FBS93/STM32WLE5_RF_dongle/sw/arch/sw_parameters.md

# sw_parameters

## SW_ARCH_PARAMETER_1

Name: swp_rfSemanticParameters

Parameter inherited from upstream definition.

Upstream traceability:
- [SW_REQ_PARAMETER_1](../req/sw_parameters.md#sw_req_parameter_1)

Status: approved
