FBS93/STM32WLE5_RF_dongle/sys/arch/sys_interfaces.md

# sys_interfaces

## SYS_ARCH_INTERFACE_1

Name: sysi_usbExternal

Interface inherited from upstream definition.

Upstream traceability:
- [SYS_REQ_INTERFACE_1](../req/sys_interfaces.md#sys_req_interface_1)

Status: approved

## SYS_ARCH_INTERFACE_2

Name: sysi_rfExternal

Interface inherited from upstream definition.

Upstream traceability:
- [SYS_REQ_INTERFACE_2](../req/sys_interfaces.md#sys_req_interface_2)

Status: approved
