FBS93/STM32WLE5_RF_dongle/sys/arch/sys_parameters.md

# sys_parameters

## SYS_ARCH_PARAMETER_1

Name: sysp_packetType

Parameter inherited from upstream definition.

Upstream traceability:
- [SYS_REQ_PARAMETER_1](../req/sys_parameters.md#sys_req_parameter_1)

Status: approved

## SYS_ARCH_PARAMETER_2

Name: sysp_rfFrequencyHz

Parameter inherited from upstream definition.

Upstream traceability:
- [SYS_REQ_PARAMETER_2](../req/sys_parameters.md#sys_req_parameter_2)

Status: approved

## SYS_ARCH_PARAMETER_3

Name: sysp_payloadLengthBytes

Parameter inherited from upstream definition.

Upstream traceability:
- [SYS_REQ_PARAMETER_3](../req/sys_parameters.md#sys_req_parameter_3)

Status: approved

## SYS_ARCH_PARAMETER_4

Name: sysp_loraSpreadingFactor

Parameter inherited from upstream definition.

Upstream traceability:
- [SYS_REQ_PARAMETER_4](../req/sys_parameters.md#sys_req_parameter_4)

Status: approved

## SYS_ARCH_PARAMETER_5

Name: sysp_loraBandwidthKHz

Parameter inherited from upstream definition.

Upstream traceability:
- [SYS_REQ_PARAMETER_5](../req/sys_parameters.md#sys_req_parameter_5)

Status: approved

## SYS_ARCH_PARAMETER_6

Name: sysp_loraCodingRate

Parameter inherited from upstream definition.

Upstream traceability:
- [SYS_REQ_PARAMETER_6](../req/sys_parameters.md#sys_req_parameter_6)

Status: approved

## SYS_ARCH_PARAMETER_7

Name: sysp_loraLowDataRateOptimize

Parameter inherited from upstream definition.

Upstream traceability:
- [SYS_REQ_PARAMETER_7](../req/sys_parameters.md#sys_req_parameter_7)

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

Status: approved

## SYS_ARCH_PARAMETER_47

Name: sysp_radioErrors

Parameter inherited from upstream definition.

Upstream traceability:
- [SYS_REQ_PARAMETER_47](../req/sys_parameters.md#sys_req_parameter_47)

Status: approved
