FBS93/STM32WLE5_RF_dongle/sw/req/sw_cli.md

# Software CLI requirements

# SW_REQ_CLI_1

The software shall provide the host-side CLI tool defined by the applicable system CLI requirements.

Validation criteria:
- Exercise the host-side CLI against each behavior defined by the traced system CLI requirements and verify conformance without adding behavior not defined by those requirements.

Upstream traceability:
- [SYS_REQ_CLI_1](../../sys/req/sys_cli.md#sys_req_cli_1)
- [SYS_REQ_CLI_2](../../sys/req/sys_cli.md#sys_req_cli_2)
- [SYS_REQ_CLI_3](../../sys/req/sys_cli.md#sys_req_cli_3)
- [SYS_REQ_CLI_4](../../sys/req/sys_cli.md#sys_req_cli_4)
- [SYS_REQ_CLI_5](../../sys/req/sys_cli.md#sys_req_cli_5)
- [SYS_REQ_CLI_6](../../sys/req/sys_cli.md#sys_req_cli_6)
- [SYS_REQ_CLI_7](../../sys/req/sys_cli.md#sys_req_cli_7)
- [SYS_ARCH_COMPONENT_2](../../sys/arch/sys_components.md#sys_arch_component_2)
- [SYS_ARCH_INTERFACE_1](../../sys/arch/sys_interfaces.md#sys_arch_interface_1)

References:
- [SW_REQ_INTERFACE_1](sw_interfaces.md#sw_req_interface_1)

Status: approved
