FBS93/STM32WLE5_RF_dongle/sw/req/sw_interfaces.md

# Software interfaces

# SW_REQ_INTERFACE_1

Name: swi_hostUsbControl

The software shall implement the host-control interface defined by [SYS_REQ_INTERFACE_1](../../sys/req/sys_interfaces.md#sys_req_interface_1).

Upstream traceability:
- [SYS_REQ_INTERFACE_1](../../sys/req/sys_interfaces.md#sys_req_interface_1)
- [SYS_ARCH_INTERFACE_1](../../sys/arch/sys_interfaces.md#sys_arch_interface_1)
- [SYS_ARCH_COMPONENT_1](../../sys/arch/sys_components.md#sys_arch_component_1)
- [SYS_ARCH_COMPONENT_2](../../sys/arch/sys_components.md#sys_arch_component_2)
- [HW_SW_INTERFACE_7](../../hw/cross_domain_interfaces/hw_sw_interface.md#hw_sw_interface_7)

Status: approved

# SW_REQ_INTERFACE_2

Name: swi_rfInputOutput

The software shall provide the RF operation behavior through the RF interface defined by [SYS_REQ_INTERFACE_2](../../sys/req/sys_interfaces.md#sys_req_interface_2).

Upstream traceability:
- [SYS_REQ_INTERFACE_2](../../sys/req/sys_interfaces.md#sys_req_interface_2)
- [SYS_ARCH_INTERFACE_2](../../sys/arch/sys_interfaces.md#sys_arch_interface_2)
- [SYS_ARCH_COMPONENT_1](../../sys/arch/sys_components.md#sys_arch_component_1)
- [HW_SW_INTERFACE_9](../../hw/cross_domain_interfaces/hw_sw_interface.md#hw_sw_interface_9)
- [HW_SW_INTERFACE_10](../../hw/cross_domain_interfaces/hw_sw_interface.md#hw_sw_interface_10)
- [HW_SW_INTERFACE_12](../../hw/cross_domain_interfaces/hw_sw_interface.md#hw_sw_interface_12)

Status: approved
