FBS93/STM32WLE5_RF_dongle/hw/FBS_kicad_lib/3d_models/4_diode_SMD/D_0402_1005Metric.STEP

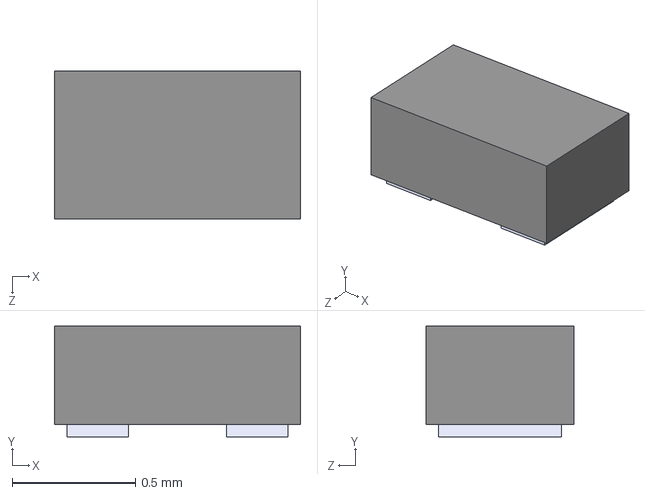
[picture p23: CAD file, 2024-11-07]
hw/FBS_kicad_lib/3d_models/4_diode_SMD/D_0402_1005Metric.STEP
1.00 x 0.45 x 0.6 mm
