FBS93/STM32WLE5_RF_dongle/hw/FBS_kicad_lib/3d_models/50_RF_filter/DLFCV-1000+.stp

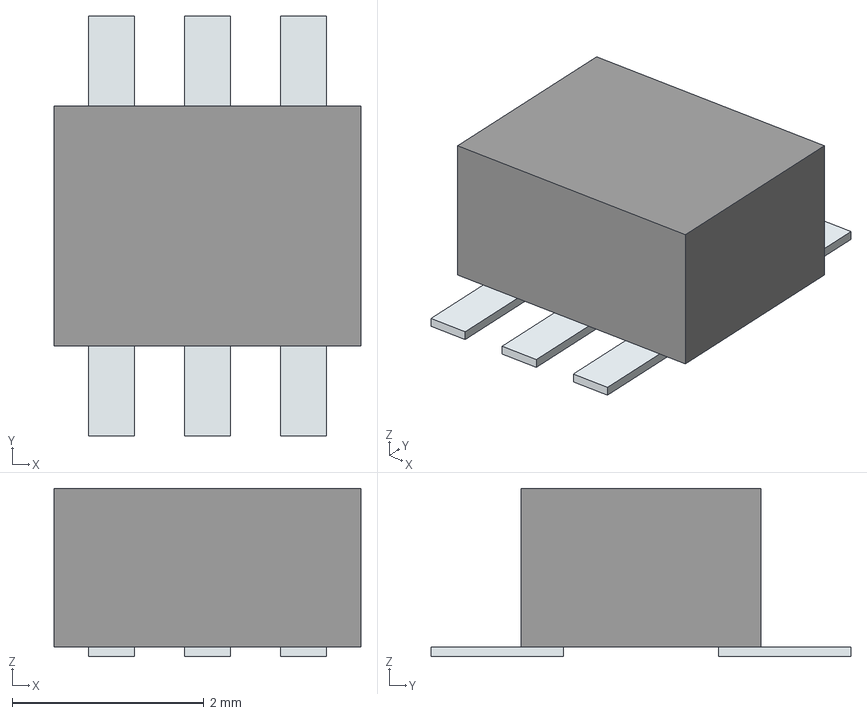
[picture p24: CAD file, 2024-11-07]
hw/FBS_kicad_lib/3d_models/50_RF_filter/DLFCV-1000+.stp
3.20 x 4.38 x 1.75 mm
Pins
