FBS93/STM32WLE5_RF_dongle/hw/FBS_kicad_lib/3d_models/5_balun_SMD/DXW21HN5011BL.stp

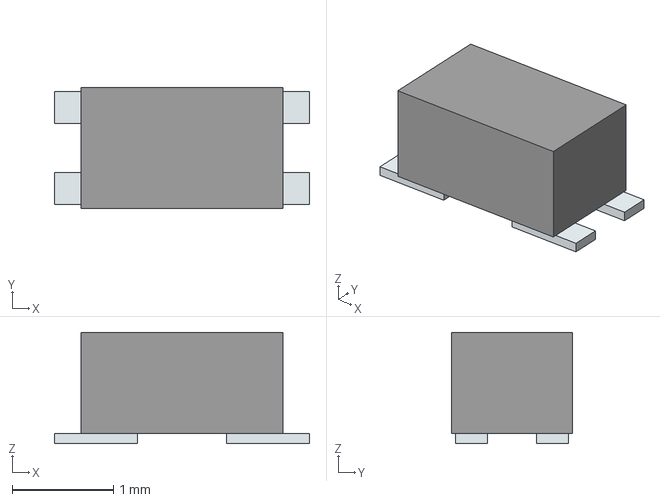
[picture p25: CAD file, 2024-11-07]
hw/FBS_kicad_lib/3d_models/5_balun_SMD/DXW21HN5011BL.stp
2.52 x 1.20 x 1.10 mm
Pins
