FBS93/STM32WLE5_RF_dongle/hw/FBS_kicad_lib/3d_models/60_RF_shield_clip/S0941_46R.stp

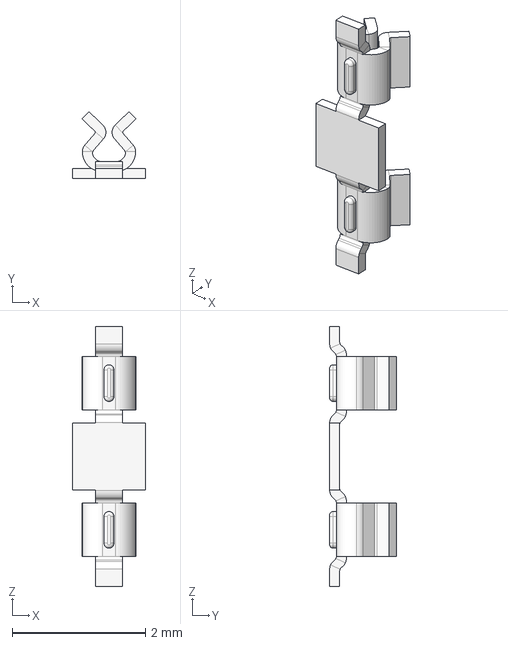
[picture p26: CAD file, 2024-11-07]
hw/FBS_kicad_lib/3d_models/60_RF_shield_clip/S0941_46R.stp
1.10 x 1.00 x 3.90 mm
