FBS93/STM32WLE5_RF_dongle/hw/FBS_kicad_lib/3d_models/6_fuse_SMD/0ZCM0020FF2G.stp

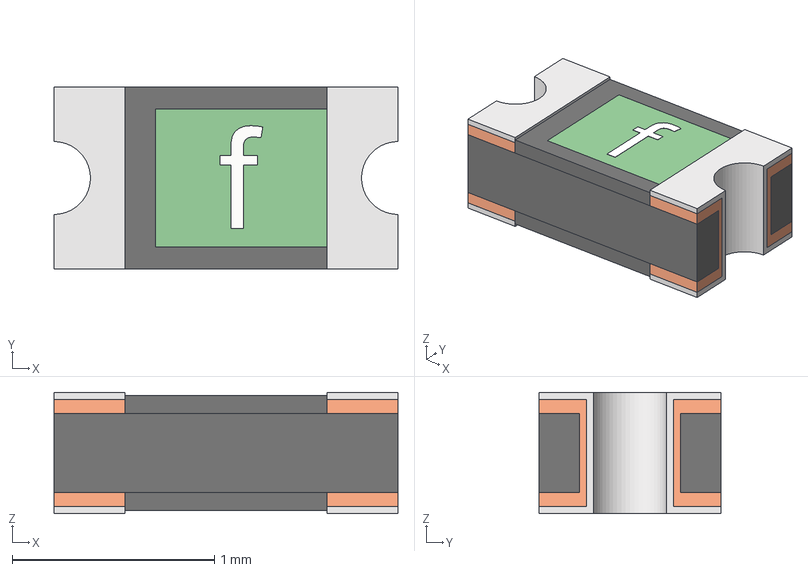
[picture p27: CAD file, 2024-11-07]
hw/FBS_kicad_lib/3d_models/6_fuse_SMD/0ZCM0020FF2G.stp
1.70 x 0.9 x 0.6 mm
0ZCM0020FF2G_PART1
0ZCM0020FF2G_PART2
0ZCM0020FF2G_PART3
0ZCM0020FF2G_PART4
0ZCM0020FF2G_PART5
0ZCM0020FF2G_PART6
0ZCM0020FF2G_PART7
0ZCM0020FF2G_PART8
0ZCM0020FF2G_PART9
0ZCM0020FF2G_PART10
0ZCM0020FF2G_PART11
