FBS93/STM32WLE5_RF_dongle/hw/FBS_kicad_lib/3d_models/105_SOT_package/SOT-23-3.step

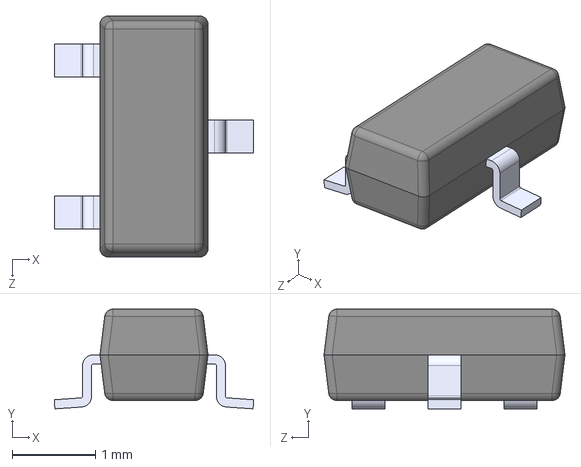
[picture p28: CAD file, 2024-11-07]
hw/FBS_kicad_lib/3d_models/105_SOT_package/SOT-23-3.step
2.40 x 1.20 x 2.90 mm
