FBS93/STM32WLE5_RF_dongle/hw/FBS_kicad_lib/3d_models/1_capacitor_SMD/C_1206_3216Metric.step

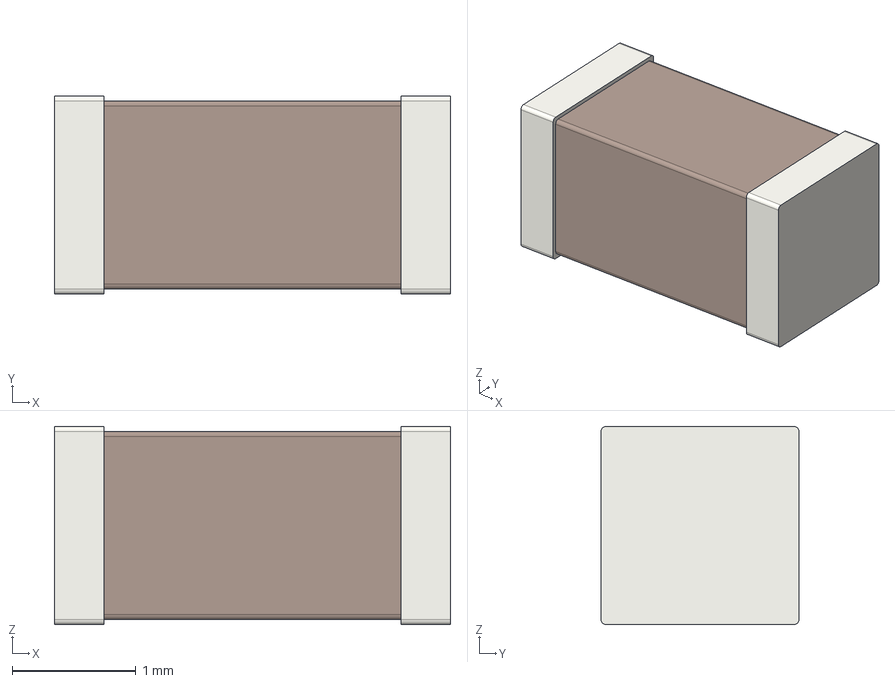
[picture p29: CAD file, 2024-11-07]
hw/FBS_kicad_lib/3d_models/1_capacitor_SMD/C_1206_3216Metric.step
3.20 x 1.60 x 1.60 mm
