FBS93/STM32WLE5_RF_dongle/hw/FBS_kicad_lib/3d_models/220_cortex-M_debug_connector/FTSH-105-01-F-DV-K.step

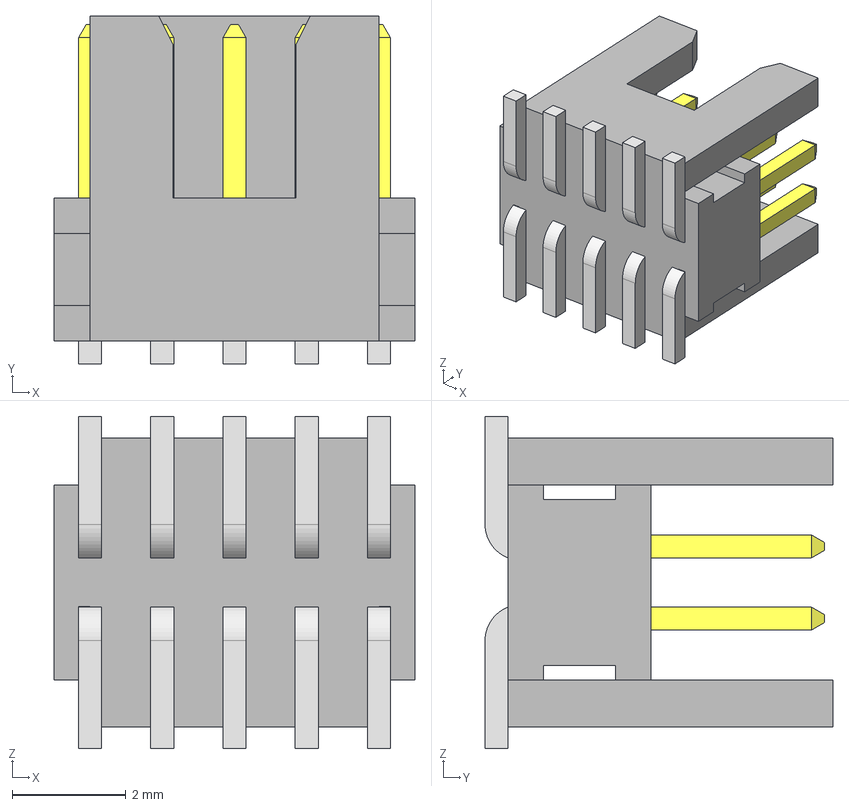
[picture p30: CAD file, 2024-11-07]
hw/FBS_kicad_lib/3d_models/220_cortex-M_debug_connector/FTSH-105-01-F-DV-K.step
6.35 x 6.12 x 5.84 mm
FTSH-105-01-F-DV-K_body
FTSH-105-01-F-DV-K_pins1
FTSH-105-01-F-DV-K_pins2
