FBS93/STM32WLE5_RF_dongle/hw/FBS_kicad_lib/3d_models/2_inductor_SMD/L_0805_2012Metric.step

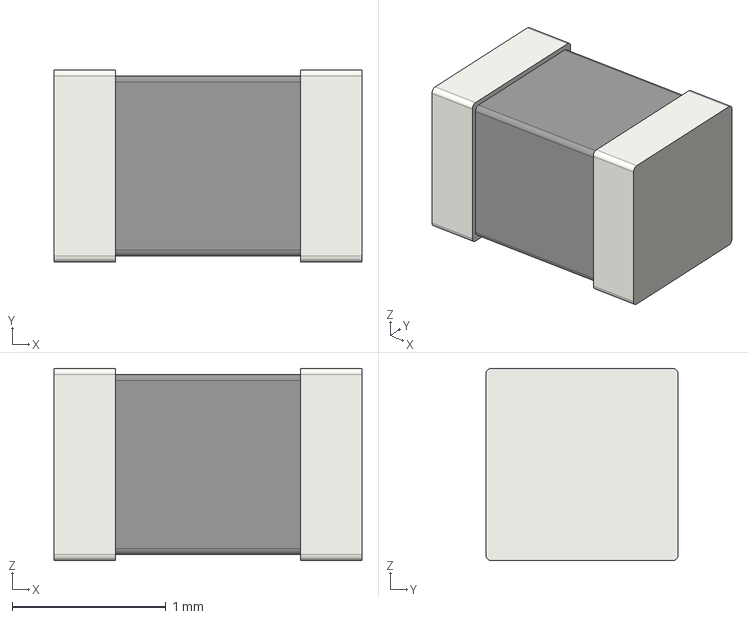
[picture p31: CAD file, 2024-11-07]
hw/FBS_kicad_lib/3d_models/2_inductor_SMD/L_0805_2012Metric.step
2.00 x 1.25 x 1.25 mm
