FBS93/STM32WLE5_RF_dongle/hw/FBS_kicad_lib/3d_models/300_pin_header_connector/PinHeader_1x02_P2.54mm_Vertical.step

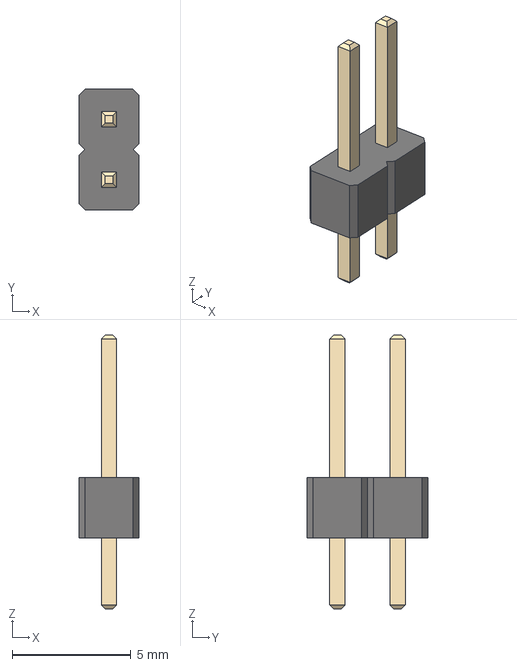
[picture p32: CAD file, 2024-11-07]
hw/FBS_kicad_lib/3d_models/300_pin_header_connector/PinHeader_1x02_P2.54mm_Vertical.step
2.54 x 5.08 x 11.5 mm
