FBS93/STM32WLE5_RF_dongle/hw/FBS_kicad_lib/3d_models/4_diode_SMD/ESDALC6V1-1U2.step

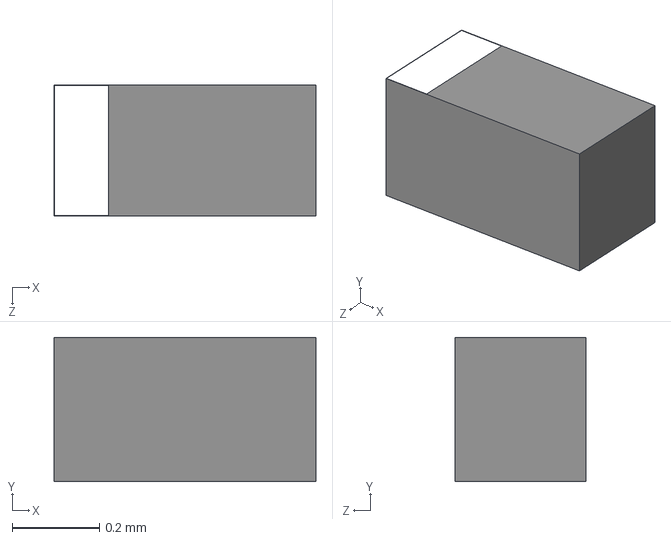
[picture p33: CAD file, 2024-11-07]
hw/FBS_kicad_lib/3d_models/4_diode_SMD/ESDALC6V1-1U2.step
0.6 x 0.33 x 0.3 mm
