FBS93/STM32WLE5_RF_dongle/hw/FBS_kicad_lib/3d_models/6_fuse_SMD/Fuse_0603_1608Metric.step

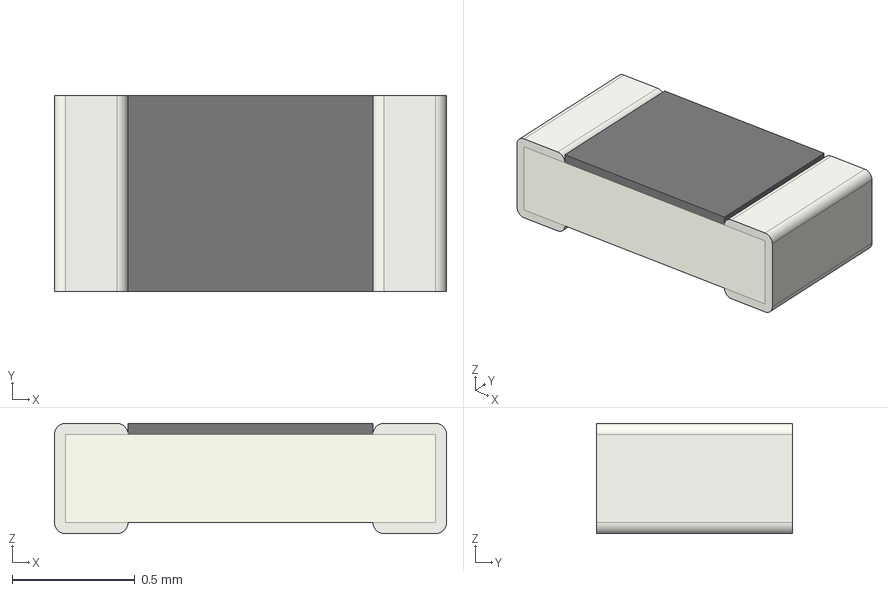
[picture p34: CAD file, 2024-11-07]
hw/FBS_kicad_lib/3d_models/6_fuse_SMD/Fuse_0603_1608Metric.step
1.60 x 0.8 x 0.45 mm
