FBS93/STM32WLE5_RF_dongle/hw/FBS_kicad_lib/3d_models/105_SOT_package/SOT-23-5.step

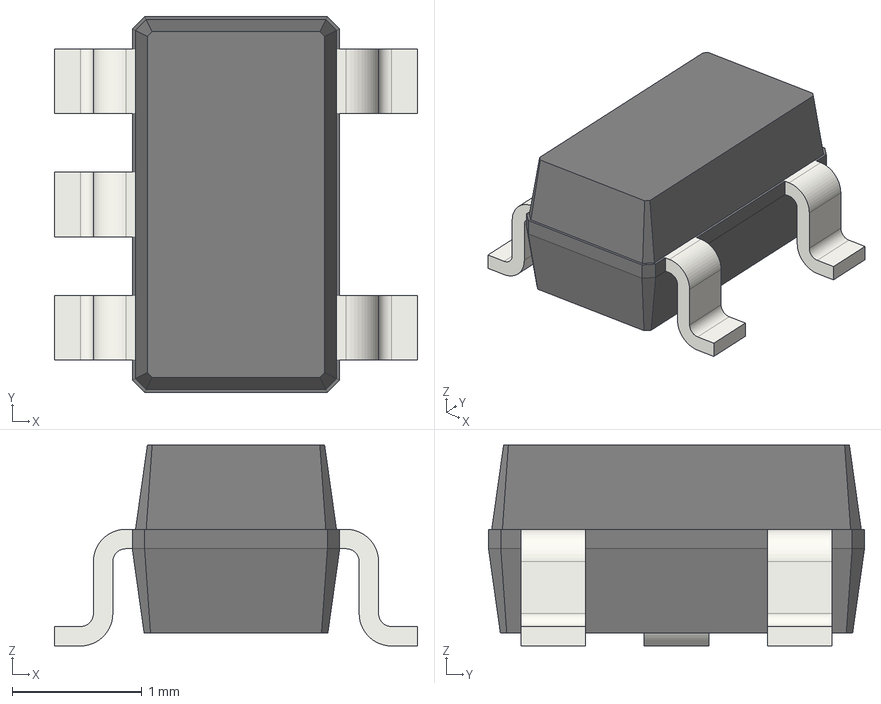
[picture p35: CAD file, 2024-11-07]
hw/FBS_kicad_lib/3d_models/105_SOT_package/SOT-23-5.step
2.80 x 2.90 x 1.55 mm
