FBS93/STM32WLE5_RF_dongle/hw/FBS_kicad_lib/3d_models/1_capacitor_SMD/C_0402_1005Metric.step

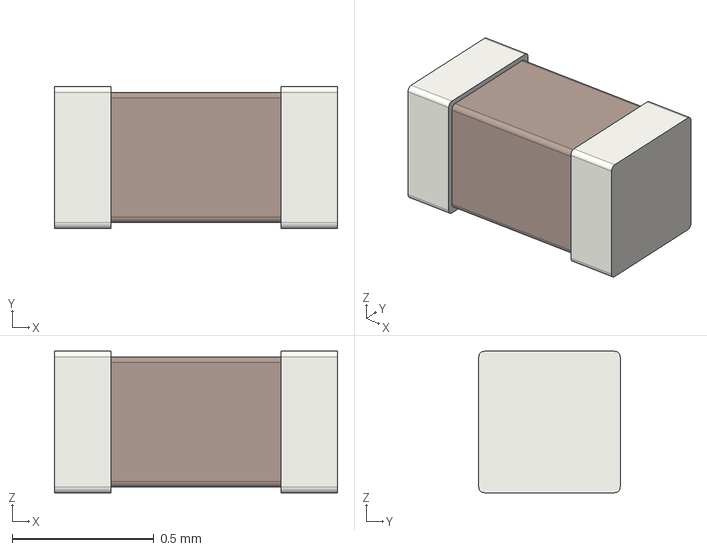
[picture p36: CAD file, 2024-11-07]
hw/FBS_kicad_lib/3d_models/1_capacitor_SMD/C_0402_1005Metric.step
1.00 x 0.5 x 0.5 mm
