FBS93/STM32WLE5_RF_dongle/hw/FBS_kicad_lib/3d_models/300_pin_header_connector/PinHeader_1x08_P2.54mm_Vertical.step

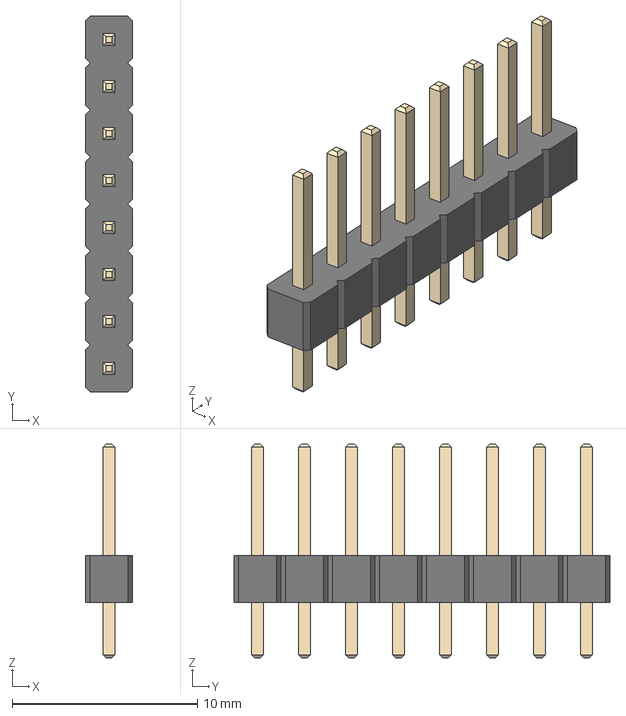
[picture p37: CAD file, 2024-11-07]
hw/FBS_kicad_lib/3d_models/300_pin_header_connector/PinHeader_1x08_P2.54mm_Vertical.step
2.54 x 20.3 x 11.5 mm
