FBS93/STM32WLE5_RF_dongle/hw/FBS_kicad_lib/3d_models/105_SOT_package/SOT-363.step

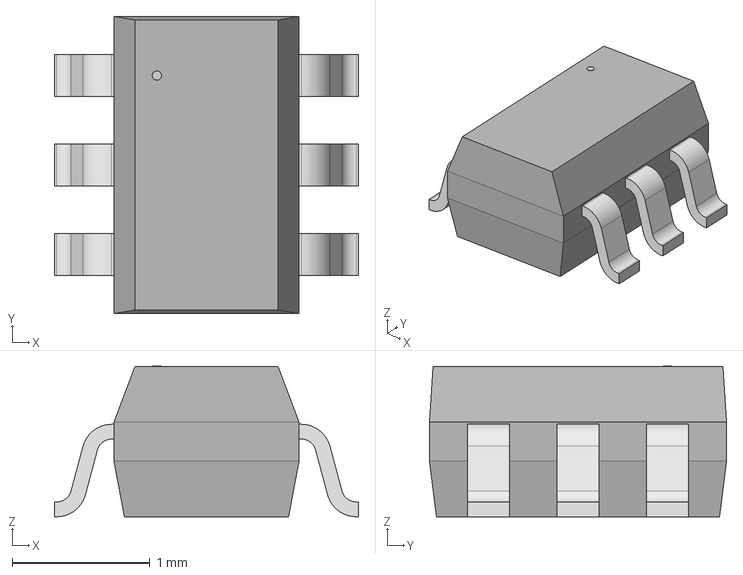
[picture p38: CAD file, 2024-11-07]
hw/FBS_kicad_lib/3d_models/105_SOT_package/SOT-363.step
2.21 x 2.16 x 1.09 mm
