FBS93/STM32WLE5_RF_dongle/doc/development_methodology/software_domain/resources/assembler_format_tool.md

# Assembler format tool

## Overview

This document describes the assembler formatting tool used by the software domain to normalize GNU assembler source files (`.S`) in a consistent way across the repository.

The underlying tool is documented in [../../../../tools/asm_format/asm_format.md](../../../../tools/asm_format/asm_format.md).
