FBS93/STM32WLE5_RF_dongle/software/stm32wle5_rf_dongle_example/firmware/Core/Src/main.c

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
/* Includes ------------------------------------------------------------------*/
#include "main.h"
#include "app_subghz_phy.h"

/* USER CODE BEGIN Includes */
#include "app.h"
/* USER CODE END Includes */

SUBGHZ_HandleTypeDef hsubghz;

UART_HandleTypeDef huart2;

void SystemClock_Config(void);
static void MX_GPIO_Init(void);
static void MX_USART2_UART_Init(void);
/* USER CODE BEGIN 0 */

int main(void)
{
  /* Initialization calls that shall be done in main() due to ST generated code architecture... */
  /* ------------------------------------------------------------------------------------------ */
  /* Reset of all peripherals, Initializes the Flash interface and the Systick. */
  HAL_Init();

  /* Configure the system clock */
  SystemClock_Config();

  /* Initialize all configured peripherals */
  MX_GPIO_Init();
  MX_USART2_UART_Init();
  /* ------------------------------------------------------------------------------------------ */

  app_init();

  while (1)
  {
    app_executePeriodicTask();
  }

  return 0;
}

/* USER CODE END 0 */

/**
  * @brief  The application entry point.
  * @retval int
  */

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
